sadaoikebe/tc69/firmware/sketch_keyboard/sketch_keyboard.h

#ifndef __NICOLA_KEYBOARD_H__
#define __NICOLA_KEYBOARD_H__

typedef unsigned char uint8_t;
typedef unsigned short uint16_t;
typedef unsigned short matrix_row_t;

const int MATRIX_ROWS = 5;
const int MATRIX_COLS = 16;

//const int ROWS[] = { 2, 4, 1, 0, 7 };
//const int COLS[] = { 3, 6, 27, 26 };
//const int PURGE = 28;
//const int SENSE = 29;
// samd21
const int PURGE = 2;
const int SENSE = 3;
const int ROWS[] = { 8, 9, 7, 6, 5 };
const int COLS[] = { 10, 4, 1, 0 };

// sense.in
void calibrate_adc(void);
void acquire_adc(int adc_measured_val[][5]);
uint8_t matrix_scan(void);
matrix_row_t matrix_get_row(uint8_t row);

// nicola.ino
void nicola_on(void);
void nicola_off(void);
bool nicola_state(void);
void nicola_clear(void);
bool is_nicola_layer(uint16_t keycode, bool pressed);
bool process_nicola(uint16_t keycode, bool pressed);

#endif
